funkonaut/Earrings/design_files/Alien/Alien_dark.jpg

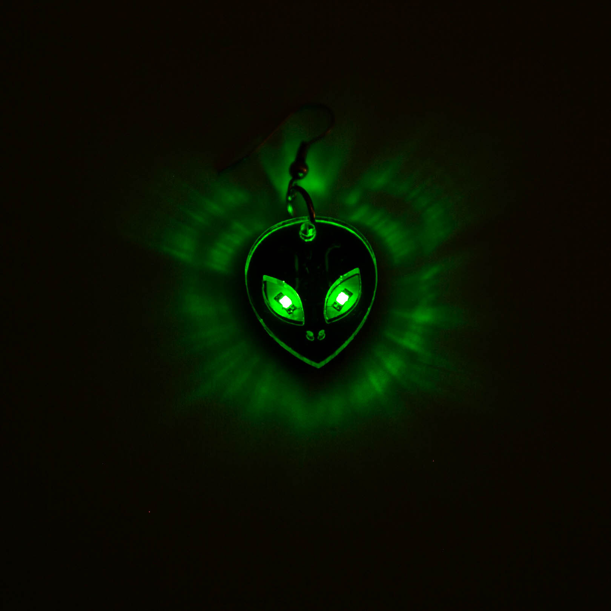
design_files/Alien/Alien_dark.jpg
