funkonaut/Earrings/design_files/Alien/alien_sch.png

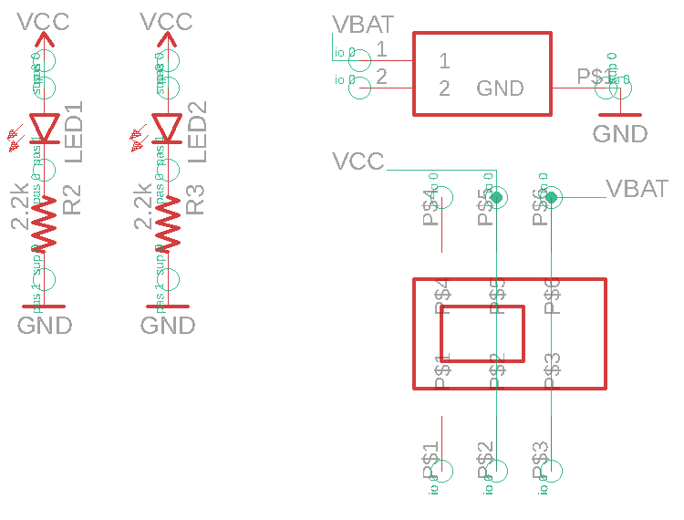
design_files/Alien/alien_sch.png
