funkonaut/Earrings/design_files/Angel/angel_dim_brd.png

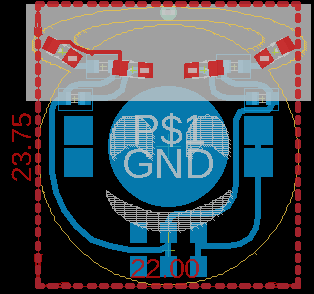
design_files/Angel/angel_dim_brd.png
