funkonaut/Earrings/design_files/Angel/angel_sch.png

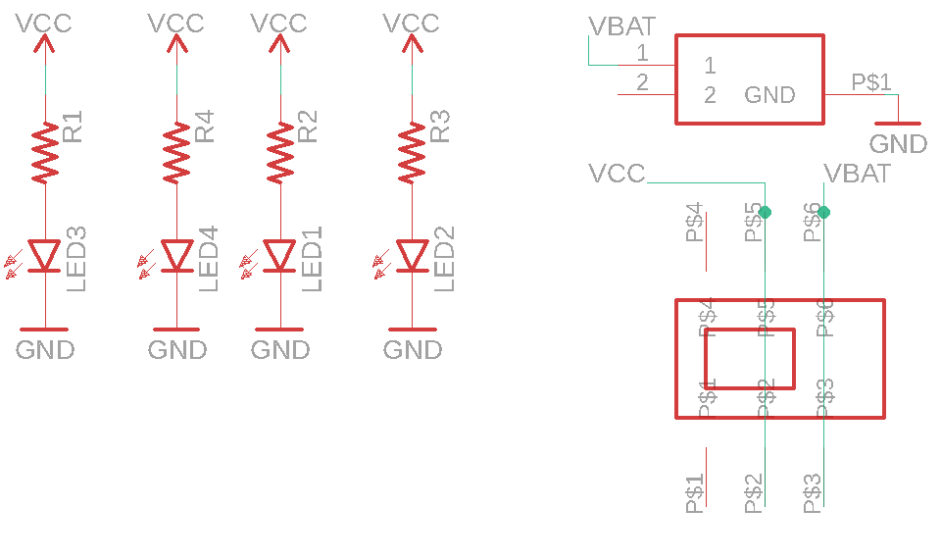
design_files/Angel/angel_sch.png
