funkonaut/Earrings/design_files/Cross/cross_brd.png

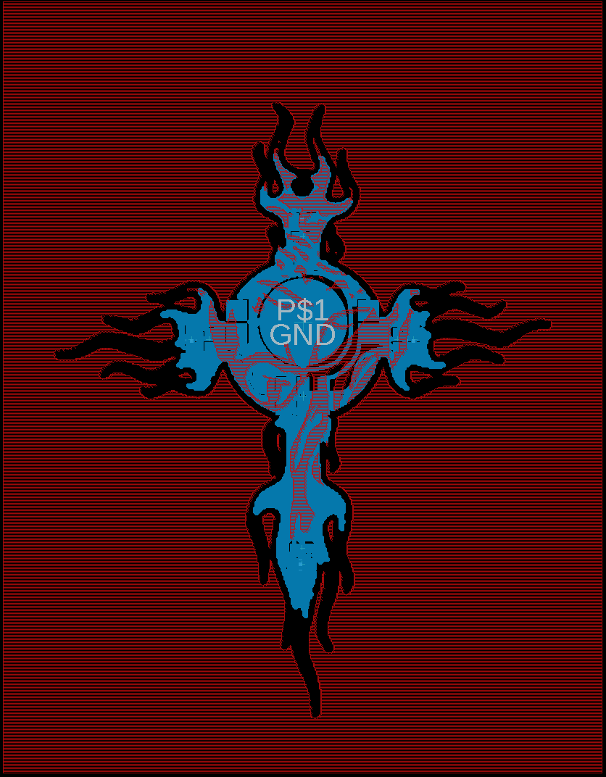
design_files/Cross/cross_brd.png
