funkonaut/Earrings/design_files/Cross/cross_dim_brd.png

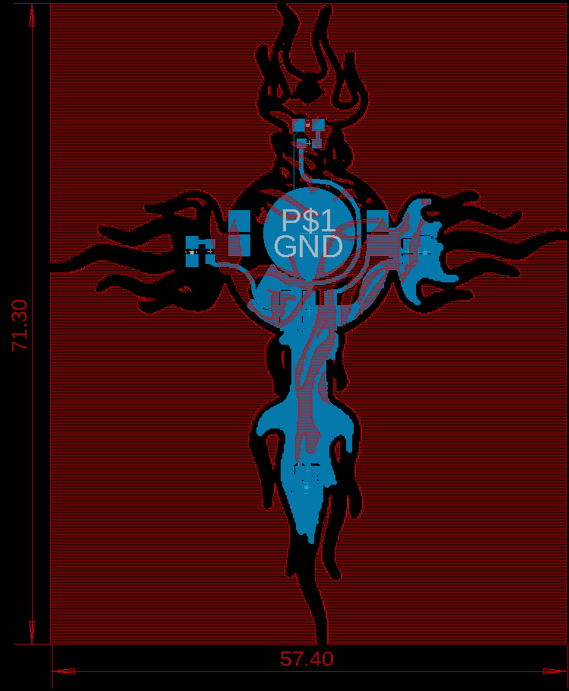
design_files/Cross/cross_dim_brd.png
