funkonaut/Earrings/design_files/Cross/cross_sch.png

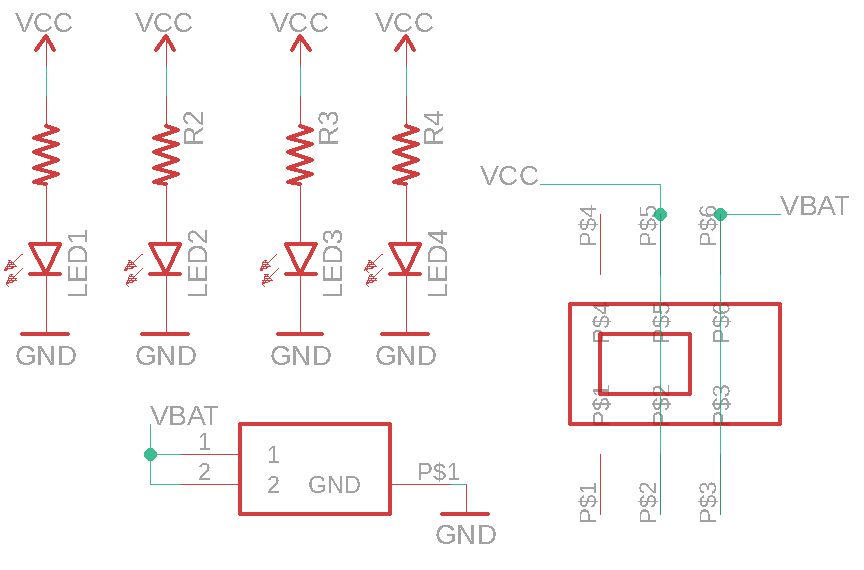
design_files/Cross/cross_sch.png
