funkonaut/Earrings/design_files/Devil/devil_brd.png

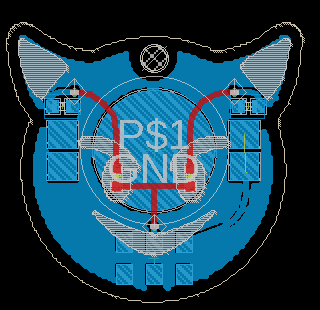
design_files/Devil/devil_brd.png
