funkonaut/Earrings/design_files/Skull/skull_black_brd.png

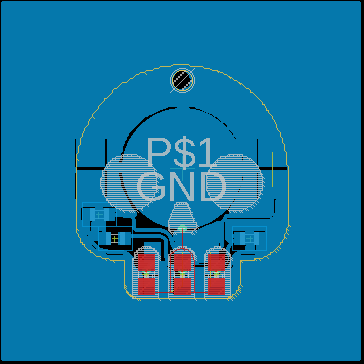
design_files/Skull/skull_black_brd.png
