funkonaut/Earrings/design_files/Skull/skull_sch.png

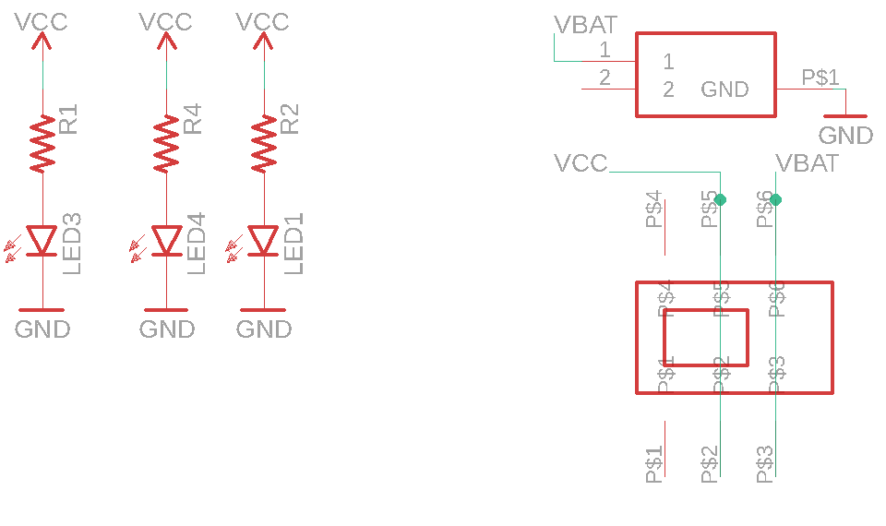
design_files/Skull/skull_sch.png
