funkonaut/Earrings/design_files/Skull/skull_white_brd.png

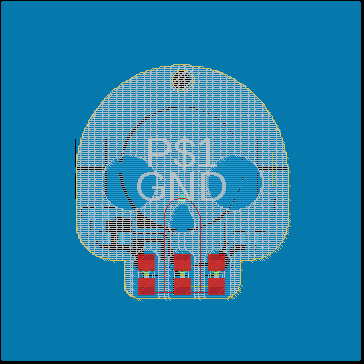
design_files/Skull/skull_white_brd.png
