funkonaut/Earrings/design_files/Texas/texas_brd.png

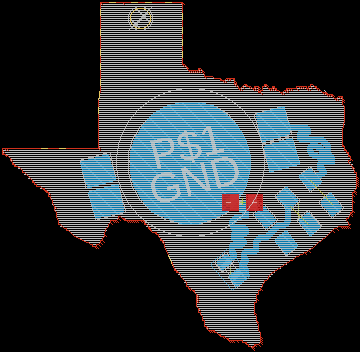
design_files/Texas/texas_brd.png
