funkonaut/Earrings/design_files/Texas/texas_dim_brd.png

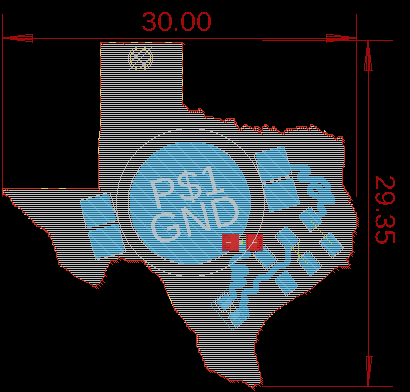
design_files/Texas/texas_dim_brd.png
