funkonaut/Earrings/design_files/Texas/texas_sch.png

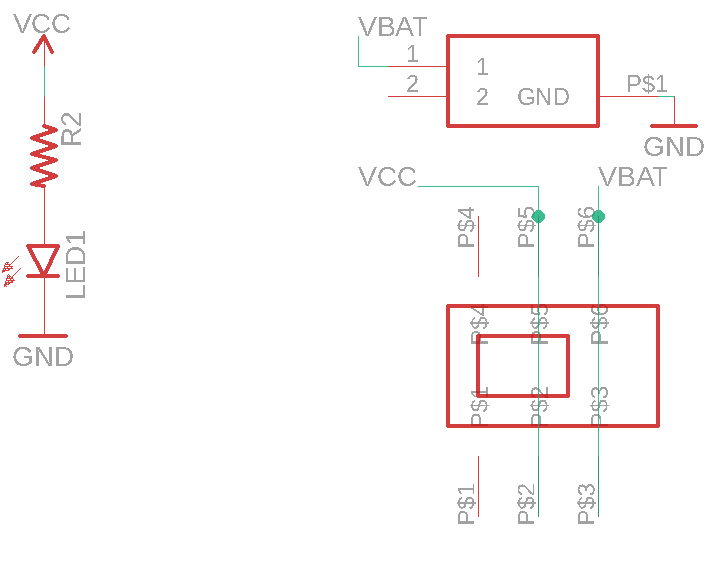
design_files/Texas/texas_sch.png
